Julio2083478/WaterMeterIA/Software/Interfaz/visualizacion/4_7_2023_21.jpg

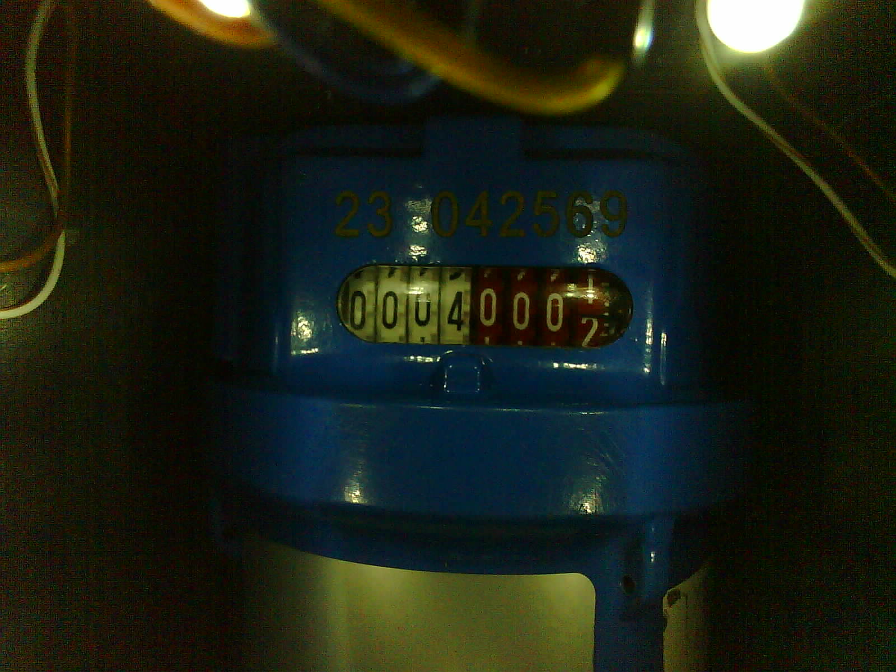
Software/Interfaz/visualizacion/4_7_2023_21.jpg
